LittleRescuer/RLP2024/img/2.jpg

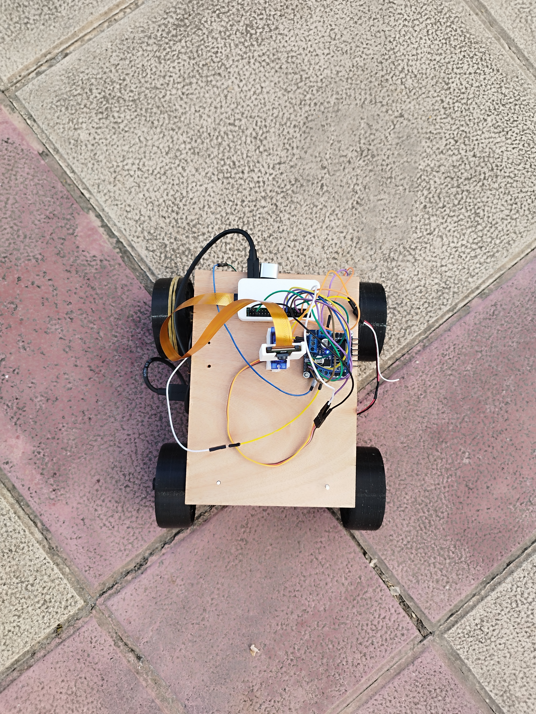
img/2.jpg
