LittleRescuer/RLP2024/img/3.jpg

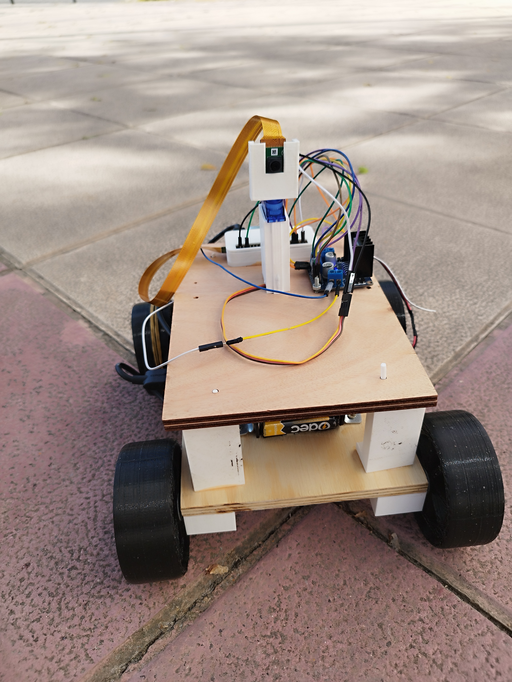
img/3.jpg
