LittleRescuer/RLP2024/img/4.jpg

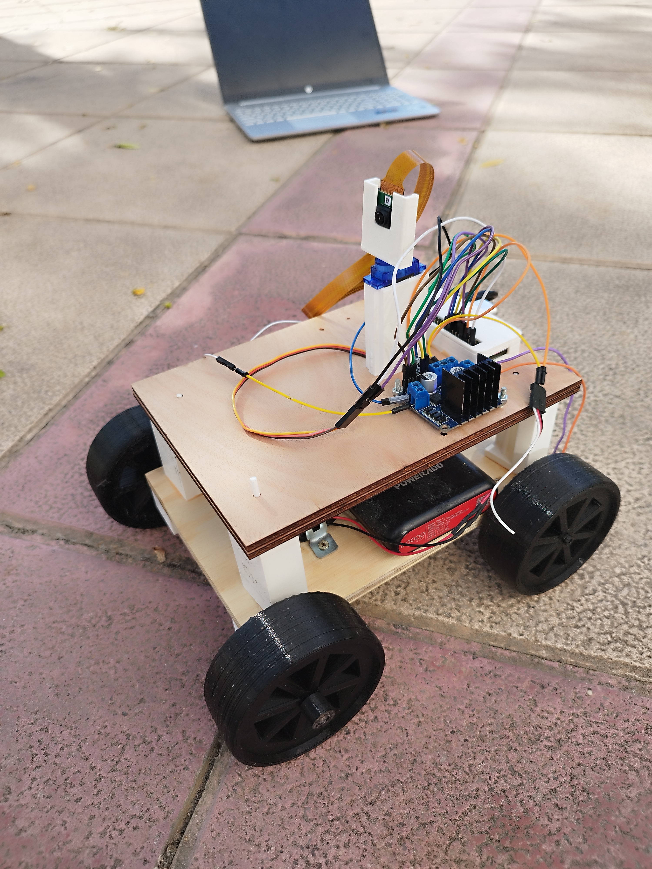
img/4.jpg
