LittleRescuer/RLP2024/img/5.jpg

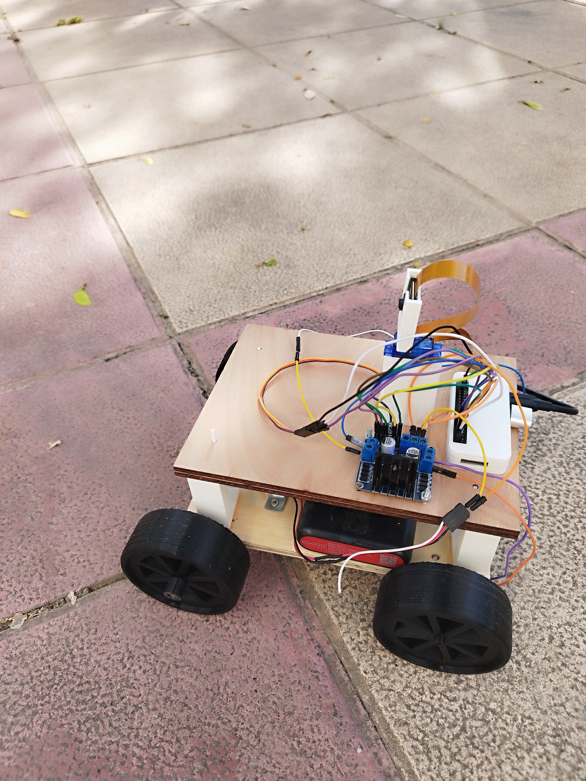
img/5.jpg
