LittleRescuer/RLP2024/img/6.jpg

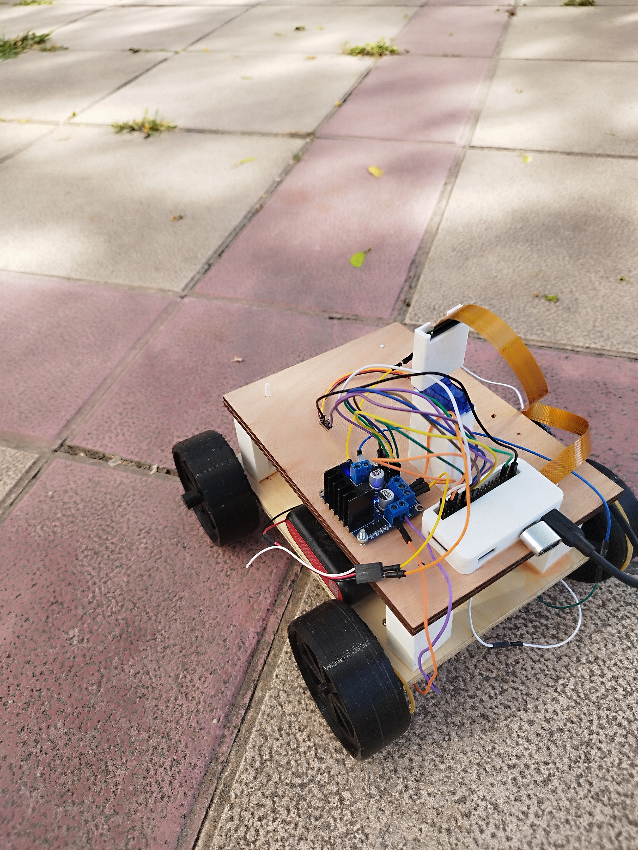
img/6.jpg
